MicrochipTech/EERAM-Rally-Mini-Demo/Firmware/EERAM_Mini_Demo.X/images.c

#include "litegui.h"


const IMAGE16X26 car16 = {
    16, 26, 2, 1,
    {
        0x10, 0x84, 0x10, 0x84, 0x10, 0x84, 0x10, 0x84, 0x10, 0x84, 0x10, 0x84, 0x10, 0x84, 0x10, 0x84, 0x10, 0x84, 0x10, 0x84, 0x10, 0x84, 0x10, 0x84, 0x10, 0x84, 0x10, 0x84, 0x10, 0x84, 0x10, 0x84,
        0x10, 0x84, 0x10, 0x84, 0x30, 0x7c, 0x49, 0xba, 0x09, 0xda, 0x87, 0xd1, 0x87, 0xd1, 0x87, 0xd1, 0x87, 0xd1, 0x87, 0xd1, 0x87, 0xd9, 0x29, 0xc2, 0x30, 0x7c, 0x10, 0x84, 0x10, 0x84, 0x10, 0x84,
        0x10, 0x84, 0x10, 0x84, 0x10, 0x84, 0xe8, 0xe1, 0x83, 0xf8, 0x63, 0xf8, 0x83, 0xf8, 0xc4, 0xf0, 0xa3, 0xf8, 0x63, 0xf8, 0x83, 0xf8, 0xa7, 0xe9, 0x10, 0x84, 0x10, 0x84, 0x10, 0x84, 0x10, 0x84,
        0x10, 0x84, 0x10, 0x84, 0x61, 0x08, 0x00, 0x18, 0x45, 0x49, 0xf0, 0x93, 0x6a, 0xba, 0x83, 0xf8, 0x29, 0xc2, 0xf0, 0x93, 0x86, 0x51, 0x00, 0x18, 0x41, 0x00, 0x10, 0x84, 0x10, 0x84, 0x10, 0x84,
        0x10, 0x84, 0x10, 0x84, 0x00, 0x00, 0x00, 0x00, 0x66, 0x29, 0xb2, 0x84, 0xcb, 0xb2, 0x63, 0xf8, 0x8b, 0xba, 0xb2, 0x84, 0xc7, 0x31, 0x00, 0x00, 0x00, 0x00, 0x10, 0x84, 0x10, 0x84, 0x10, 0x84,
        0x10, 0x84, 0x10, 0x84, 0x00, 0x00, 0x00, 0x00, 0x25, 0x29, 0xcf, 0x73, 0x4a, 0xa2, 0x83, 0xf8, 0x29, 0xb2, 0xcf, 0x6b, 0x66, 0x31, 0x00, 0x00, 0x00, 0x00, 0x10, 0x84, 0x10, 0x84, 0x10, 0x84,
        0x10, 0x84, 0x10, 0x84, 0x00, 0x00, 0x00, 0x00, 0x00, 0x00, 0x00, 0x00, 0x00, 0x58, 0x05, 0xf9, 0x00, 0x68, 0x00, 0x00, 0x00, 0x00, 0x00, 0x00, 0x00, 0x00, 0x10, 0x84, 0x10, 0x84, 0x10, 0x84,
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
    },
};
