MicrochipTech/EERAM-Rally-Mini-Demo/Firmware/EERAM_Mini_Demo.X/mchp_meatball.c

/* GIMP RGBA C-Source image dump (mchp_meatball.c) */

#include "litegui.h"

 const IMAGE70x65 mchp_meatball = {
  70, 65, 2, 1,
  "\000\000\000\000\000\000\000\000\000\000\000\000\000\000\000\000\000\000\000\000\000\000\000\000\000\000\000\000\000\000\000\000\000\000\000\000"
  "\000\000\000\000\000\000\000\000\000\000\000\000\000\000\000\000\000\000\000\000\040\030A\070\202`\202p\202p\202p\202"
  "p\202p\202p\202p\202pA\070\040\030\000\000\000\000\000\000\000\000\000\000\000\000\000\000\000\000\000\000\000\000\000"
  "\000\000\000\000\000\000\000\000\000\000\000\000\000\000\000\000\000\000\000\000\000\000\000\000\000\000\000\000\000\000\000\000\000\000\000\000"
  "\000\000\000\000\000\000\000\000\000\000\000\000\000\000\000\000\000\000\000\000\000\000\000\000\000\000\000\000\000\000\000\000\000\000\000\000"
  "\000\000\000\000\000\000\000\000\000\000\000\000\000\040(\202p\343\260$\331$\351$\351$\351$\351$\351"
  "$\351$\351$\351$\351$\351$\351$\351$\351$\351\343\260\202`\040(\000\000\000\000\000"
  "\000\000\000\000\000\000\000\000\000\000\000\000\000\000\000\000\000\000\000\000\000\000\000\000\000\000\000\000\000\000\000\000\000\000\000\000"
  "\000\000\000\000\000\000\000\000\000\000\000\000\000\000\000\000\000\000\000\000\000\000\000\000\000\000\000\000\000\000\000\000\000\000\000\000"
  "\000\000\000\000\000\000\000\000\000\000\000\000\000\000\000\040(\242\200\003\311$\351$\351$\351$\351$\351"
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
  "\000\000\000\000\000\000\000\000\000\000\000\000\000\000\000\000\000\000\000\000\000\000\000\000\000\000\000\000\000\000\000\000\000\000\000\000"
  "\000\000\000\000\000\000\000\000\000\000\000\000\000\000\000\000"
};
