MicrochipTech/EERAM-Rally-Mini-Demo/Firmware/EERAM_Mini_Demo.X/mcc.c

/**
  @Generated MPLAB(c) Code Configurator Source File

  @Company:
    Microchip Technology Inc.

  @File Name:
    mcc.c

  @Summary:
    This is the mcc.c file generated using MPLAB(c) Code Configurator

  @Description:
    This header file provides implementations for driver APIs for all modules selected in the GUI.
    Generation Information :
        Product Revision  :  MPLAB(c) Code Configurator - 4.0
        Device            :  PIC18F47K40
        Driver Version    :  1.02
    The generated drivers are tested against the following:
        Compiler          :  XC8 1.35
        MPLAB             :  MPLAB X 3.40
*/

/*
    (c) 2016 Microchip Technology Inc. and its subsidiaries. You may use this
    software and any derivatives exclusively with Microchip products.

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
    IN NO EVENT WILL MICROCHIP BE LIABLE FOR ANY INDIRECT, SPECIAL, PUNITIVE,
    INCIDENTAL OR CONSEQUENTIAL LOSS, DAMAGE, COST OR EXPENSE OF ANY KIND
    WHATSOEVER RELATED TO THE SOFTWARE, HOWEVER CAUSED, EVEN IF MICROCHIP HAS
    BEEN ADVISED OF THE POSSIBILITY OR THE DAMAGES ARE FORESEEABLE. TO THE
    FULLEST EXTENT ALLOWED BY LAW, MICROCHIP'S TOTAL LIABILITY ON ALL CLAIMS IN
    ANY WAY RELATED TO THIS SOFTWARE WILL NOT EXCEED THE AMOUNT OF FEES, IF ANY,
    THAT YOU HAVE PAID DIRECTLY TO MICROCHIP FOR THIS SOFTWARE.

    MICROCHIP PROVIDES THIS SOFTWARE CONDITIONALLY UPON YOUR ACCEPTANCE OF THESE
    TERMS.
*/

// Configuration bits: selected in the GUI

// CONFIG1L
#pragma config FEXTOSC = OFF    // External Oscillator mode Selection bits->Oscillator not enabled
#pragma config RSTOSC = HFINTOSC_64MHZ    // Power-up default value for COSC bits->HFINTOSC with HFFRQ = 64 MHz and CDIV = 1:1

// CONFIG1H
#pragma config CLKOUTEN = OFF    // Clock Out Enable bit->CLKOUT function is disabled
#pragma config CSWEN = ON    // Clock Switch Enable bit->Writing to NOSC and NDIV is allowed
#pragma config FCMEN = ON    // Fail-Safe Clock Monitor Enable bit->Fail-Safe Clock Monitor enabled

// CONFIG2L
#pragma config MCLRE = EXTMCLR    // Master Clear Enable bit->If LVP = 0, MCLR pin is MCLR; If LVP = 1, RE3 pin function is MCLR 
#pragma config PWRTE = OFF    // Power-up Timer Enable bit->Power up timer disabled
#pragma config LPBOREN = OFF    // Low-power BOR enable bit->ULPBOR disabled
#pragma config BOREN = OFF    // Brown-out Reset Enable bits->Brown-out Reset disabled

// CONFIG2H
#pragma config BORV = VBOR_2P45    // Brown Out Reset Voltage selection bits->Brown-out Reset Voltage (VBOR) set to 2.45V
#pragma config ZCD = OFF    // ZCD Disable bit->ZCD disabled. ZCD can be enabled by setting the ZCDSEN bit of ZCDCON
#pragma config PPS1WAY = OFF    // PPSLOCK bit One-Way Set Enable bit->PPSLOCK bit can be set and cleared repeatedly (subject to the unlock sequence)
#pragma config STVREN = ON    // Stack Full/Underflow Reset Enable bit->Stack full/underflow will cause Reset
#pragma config DEBUG = OFF    // Debugger Enable bit->Background debugger disabled
#pragma config XINST = OFF    // Extended Instruction Set Enable bit->Extended Instruction Set and Indexed Addressing Mode disabled

// CONFIG3L
#pragma config WDTCPS = WDTCPS_31    // WDT Period Select bits->Divider ratio 1:65536; software control of WDTPS
#pragma config WDTE = OFF    // WDT operating mode->WDT Disabled

// CONFIG3H
#pragma config WDTCWS = WDTCWS_7    // WDT Window Select bits->window always open (100%); software control; keyed access not required
#pragma config WDTCCS = SC    // WDT input clock selector->Software Control

// CONFIG4L
#pragma config WRT0 = OFF    // Write Protection Block 0->Block 0 (000800-003FFFh) not write-protected
#pragma config WRT1 = OFF    // Write Protection Block 1->Block 1 (004000-007FFFh) not write-protected
#pragma config WRT2 = OFF    // Write Protection Block 2->Block 2 (008000-00BFFFh) not write-protected
#pragma config WRT3 = OFF    // Write Protection Block 3->Block 3 (00C000-00FFFFh) not write-protected
#pragma config WRT4 = OFF    // Write Protection Block 3->Block 4 (010000-013FFFh) not write-protected
#pragma config WRT5 = OFF    // Write Protection Block 3->Block 5 (014000-017FFFh) not write-protected
#pragma config WRT6 = OFF    // Write Protection Block 3->Block 6 (018000-01BFFFh) not write-protected
#pragma config WRT7 = OFF    // Write Protection Block 3->Block 7 (01C000-01FFFFh) not write-protected

// CONFIG4H
#pragma config WRTC = OFF    // Configuration Register Write Protection bit->Configuration registers (300000-30000Bh) not write-protected
#pragma config WRTB = OFF    // Boot Block Write Protection bit->Boot Block (000000-0007FFh) not write-protected
#pragma config WRTD = OFF    // Data EEPROM Write Protection bit->Data EEPROM not write-protected
#pragma config SCANE = OFF    // Scanner Enable bit->Scanner module is NOT available for use, SCANMD bit is ignored
#pragma config LVP = ON    // Low Voltage Programming Enable bit->Low voltage programming enabled. MCLR/VPP pin function is MCLR. MCLRE configuration bit is ignored

// CONFIG5L
#pragma config CP = OFF    // UserNVM Program Memory Code Protection bit->UserNVM code protection disabled
#pragma config CPD = OFF    // DataNVM Memory Code Protection bit->DataNVM code protection disabled

// CONFIG6L
#pragma config EBTR0 = OFF    // Table Read Protection Block 0->Block 0 (000800-003FFFh) not protected from table reads executed in other blocks
#pragma config EBTR1 = OFF    // Table Read Protection Block 1->Block 1 (004000-007FFFh) not protected from table reads executed in other blocks
#pragma config EBTR2 = OFF    // Table Read Protection Block 2->Block 2 (008000-00BFFFh) not protected from table reads executed in other blocks
#pragma config EBTR3 = OFF    // Table Read Protection Block 3->Block 3 (00C000-00FFFFh) not protected from table reads executed in other blocks
#pragma config EBTR4 = OFF    // Table Read Protection Block 4->Block 4 (010000-013FFFh) not protected from table reads executed in other blocks
#pragma config EBTR5 = OFF    // Table Read Protection Block 5->Block 5 (014000-017FFFh) not protected from table reads executed in other blocks
#pragma config EBTR6 = OFF    // Table Read Protection Block 6->Block 6 (018000-01BFFFh) not protected from table reads executed in other blocks
#pragma config EBTR7 = OFF    // Table Read Protection Block 7->Block 7 (01C000-01FFFFh) not protected from table reads executed in other blocks

// CONFIG6H
#pragma config EBTRB = OFF    // Boot Block Table Read Protection bit->Boot Block (000000-0007FFh) not protected from table reads executed in other blocks

#include "mcc.h"
#include "hardware.h"

void SYSTEM_Initialize(void)
{
    
    //INTERRUPT_Initialize();
    //PIN_MANAGER_Initialize();
    OSCILLATOR_Initialize();
    //CCP1_Initialize();
    //TMR3_Initialize();
    //TMR1_Initialize();
    //CWG_Initialize();
    
    //I2C2_Initialize();
    //SPI1_Initialize();
    
    // *** put this where it belongs later ************************************
    // Turn all analog to Digital pins
    ANSELA=0;
    ANSELB=0;
    ANSELC=0;
    ANSELD=0;
    ANSELE=0;
  
    // Enable Pull ups on I2C lines - RB1/RB2
    //WPUB=0xFF; // Did this because bit wise manipulation did not work

    // Hardware driven I2C pins
    TRISBbits.TRISB1=1;
    TRISBbits.TRISB2=1;
    
    // *** do PPS stuff *******************************************************
    // Unlock PPS
    PPS_UNLOCK();
    
    SPI_CLK_PPS();
    SPI_MOSI_PPS();
    SPI_MISO_PPS();
    T4INPPS = 0x16;
    
    PWM_PPS();
    
    // Lock PPS
    PPS_LOCK();
    // ************************************************************************
    
    // *** TMR3 1 ms timer ****************************************************
    T3CON=0;
    TMR3H=TMR1RELOADH;
    TMR3L=TMR1RELOADL;
    T3CLK  = 0b00000001;  // Fosc / 4
    T3GCON = 0b00000000;  // Gate control OFF
    T3CON  = 0b00110011;  // Pre 1:8 Timer 1 ON
    TMR3IF=0;
    TMR3IE=1;
    // ************************************************************************

    // Turn Backlight on    
    BACKLIGHT_TRIS=0;
    BACKLIGHT_ON();
    // ************************************************************************
}

void OSCILLATOR_Initialize(void)
{
    // NOSC HFINTOSC; NDIV 1; 
    OSCCON1 = 0x60;
    // CSWHOLD may proceed; SOSCPWR Low power; 
    OSCCON3 = 0x00;
    // MFOEN disabled; LFOEN disabled; ADOEN disabled; SOSCEN disabled; EXTOEN disabled; HFOEN disabled; 
    OSCEN = 0x00;
    // HFFRQ 64_MHz; 
    OSCFRQ = 0x08;
    // TUN 0; 
    OSCTUNE = 0x00;
    // Set the secondary oscillator
    
}


/**
 End of File
*/
