MicrochipTech/EERAM-Rally-Mini-Demo/Firmware/EERAM_Mini_Demo.X/spi1.c

/**
  SPI1 Generated Driver File

  @Company
    Microchip Technology Inc.

  @File Name
    spi1.c

  @Summary
    This is the generated driver implementation file for the SPI1 driver using PIC10 / PIC12 / PIC16 / PIC18 MCUs

  @Description
    This header file provides implementations for driver APIs for SPI1.
    Generation Information :
        Product Revision  :  PIC10 / PIC12 / PIC16 / PIC18 MCUs - 1.78
        Device            :  PIC18F47K40
        Driver Version    :  1.0.0
    The generated drivers are tested against the following:
        Compiler          :  XC8 2.05 and above or later
        MPLAB             :  MPLAB X 5.20
 */

/*
    (c) 2018 Microchip Technology Inc. and its subsidiaries. 
    
    Subject to your compliance with these terms, you may use Microchip software and any 
    derivatives exclusively with Microchip products. It is your responsibility to comply with third party 
    license terms applicable to your use of third party software (including open source software) that 
    may accompany Microchip software.
    
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
    IN NO EVENT WILL MICROCHIP BE LIABLE FOR ANY INDIRECT, SPECIAL, PUNITIVE, 
    INCIDENTAL OR CONSEQUENTIAL LOSS, DAMAGE, COST OR EXPENSE OF ANY KIND 
    WHATSOEVER RELATED TO THE SOFTWARE, HOWEVER CAUSED, EVEN IF MICROCHIP 
    HAS BEEN ADVISED OF THE POSSIBILITY OR THE DAMAGES ARE FORESEEABLE. TO 
    THE FULLEST EXTENT ALLOWED BY LAW, MICROCHIP'S TOTAL LIABILITY ON ALL 
    CLAIMS IN ANY WAY RELATED TO THIS SOFTWARE WILL NOT EXCEED THE AMOUNT 
    OF FEES, IF ANY, THAT YOU HAVE PAID DIRECTLY TO MICROCHIP FOR THIS 
    SOFTWARE.
 */

#include "spi1.h"
#include "hardware.h"
#include <xc.h>

typedef struct {
    uint8_t con1;
    uint8_t stat;
    uint8_t add;
    uint8_t operation;
} spi1_configuration_t;

//con1 == SSPxCON1, stat == SSPxSTAT, add == SSPxADD, operation == Master/Slave
static const spi1_configuration_t spi1_configuration[] = {
    { 0xa, 0x40, 0x1, 0}
};

spi1_configuration_t mySpiConfig[] = {0xa, 0x40, 0x1, 0};

void SPI1_Initialize(void) {
    //Setup PPS Pins
    //SSP1CLKPPS = 19;// 0b00011001; // C1
    //SSP1DATPPS = 20;// 0b00100000; // D0
    // RC3PPS    = 15;
    //RC4PPS    = 16;
    //SPI setup
    SPI_MOSI_TRIS = 0;
    SPI_MISO_TRIS = 1;
    SPI_SCK_TRIS = 0;
    
    SPI_MOSI_LAT = 0;
    SPI_MISO_LAT = 0;
    SPI_SCK_LAT = 0;


    PIM_CS_TRIS = 0; //make PIM CS pin an output
    CLIK_CS_TRIS = 0;
    CLIK_CS_LAT = 1;
    PIM_CS_LAT = 1;

    SSP1STAT = 0xC0;//this seems OK for SPI Master mode
    SSP1CON1 = 0x2A;//this seems OK for SPI Master mode
    SSP1CON2 = 0x00;//This register is not used for SPI, only I2C mode
    SSP1CON3 = 0x00;//This seems OK for SPI Master mode
    SSP1ADD = 0x10;//the datasheet says values less than 3 are invalid, originally set to 0x01 by MCC
    SSP1MSK = 0x00;//SPI Master don't care
    
    
    //TRISCbits.TRISC3 = 0;
    SSP1CON1bits.SSPEN = 0;//SPI port is disabled here
}

bool SPI1_Open(void /*spi1_modes_t spi1UniqueConfiguration*/) {
    if (!SSP1CON1bits.SSPEN) {
        //SSP1STAT = spi1_configuration[spi1UniqueConfiguration].stat;
        //SSP1CON1 = spi1_configuration[spi1UniqueConfiguration].con1;
        //SSP1CON2 = 0x00;
        //SSP1ADD  = spi1_configuration[spi1UniqueConfiguration].add;

       // SSP1STAT = 0x00;
       // SSP1CON1 = 0x10;
       // SSP1CON2 = 0x00;
       // SSP1ADD = 0x03;
        //TRISCbits.TRISC3 = spi1_configuration[spi1UniqueConfiguration].operation;
        SSP1CON1bits.SSPEN = 1;//SPI port is enabled here
        return true;
    }
    return false;
}

void SPI1_Close(void) {
    SSP1CON1bits.SSPEN = 0;
}

uint8_t SPI1_ExchangeByte(uint8_t data) {
    SSP1BUF = data;
    while (!PIR3bits.SSP1IF);
    PIR3bits.SSP1IF = 0;
    return SSP1BUF;
}

void SPI1_ExchangeBlock(void *block, size_t blockSize) {
    uint8_t *data = block;
    while (blockSize--) {
        *data = SPI1_ExchangeByte(*data);
        data++;
    }
}

// Half Duplex SPI Functions

void SPI1_WriteBlock(void *block, size_t blockSize) {
    uint8_t *data = block;
    while (blockSize--) {
        SPI1_ExchangeByte(*data++);
    }
}

void SPI1_ReadBlock(void *block, size_t blockSize) {
    uint8_t *data = block;
    while (blockSize--) {
        *data++ = SPI1_ExchangeByte(0);
    }
}

void SPI1_WriteByte(uint8_t byte) {
    SSP1BUF = byte;
}

uint8_t SPI1_ReadByte(void) {
    return SSP1BUF;
}
