MicrochipTech/EERAM-Rally-Mini-Demo/Firmware/EERAM_Mini_Demo.X/liteguidrv.h

#ifndef _LIGHTGUIDRV_H
#define _LIGHTGUI_H

// lightguidrv.h
// 
// Driver for Mikes lightweight GUI for 8 bit micro-controllers
//
// Basic driver level functions that are optimized for the display
// The C file is written to be optimized for each display.
// If the display has acceleration then teh accelereation should be used.


#endif
